rnsfernando/Smart-Soldering-Staion/Enclosure-Design/Design_1/1.jpg

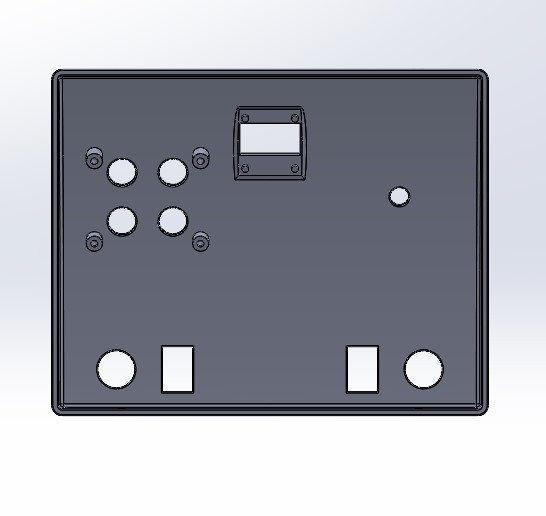
Enclosure-Design/Design_1/1.jpg
