rnsfernando/Smart-Soldering-Staion/Enclosure-Design/Design_1/2.jpg

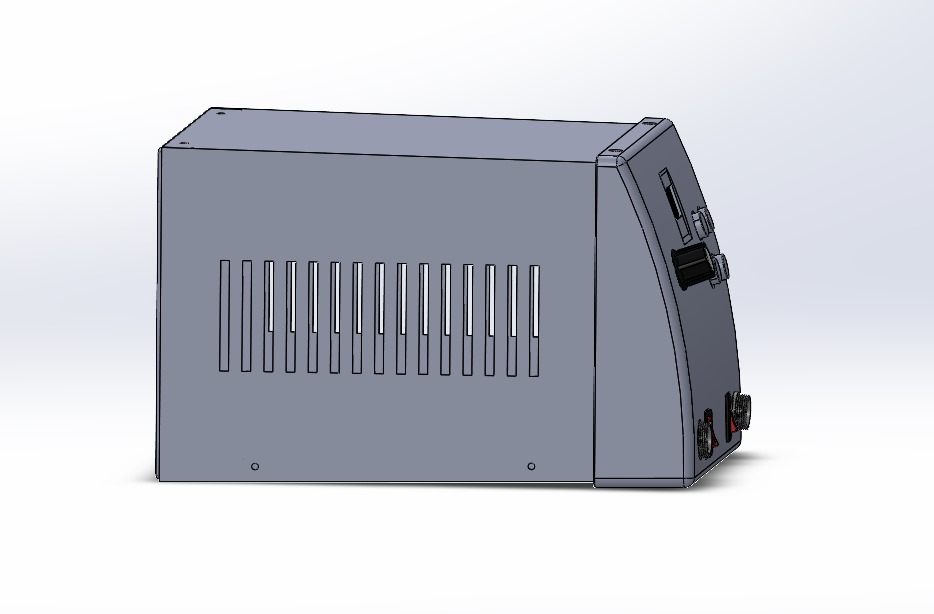
Enclosure-Design/Design_1/2.jpg
