rnsfernando/Smart-Soldering-Staion/Enclosure-Design/Design_1/3.jpg

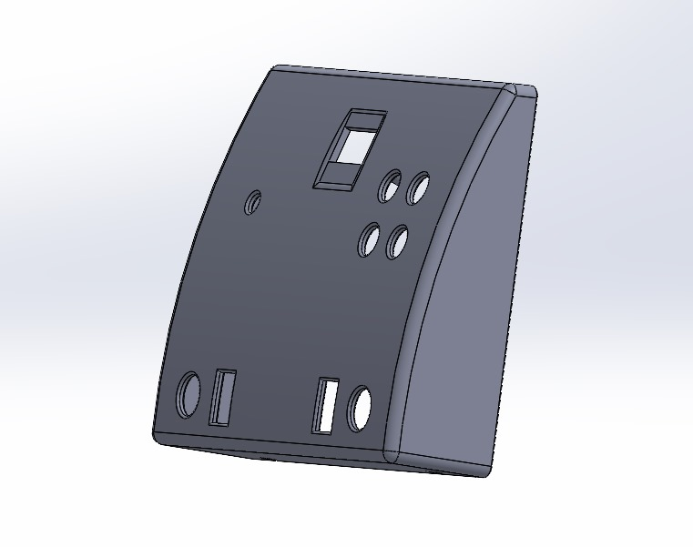
Enclosure-Design/Design_1/3.jpg
