rnsfernando/Smart-Soldering-Staion/Enclosure-Design/Design_1/4.jpg

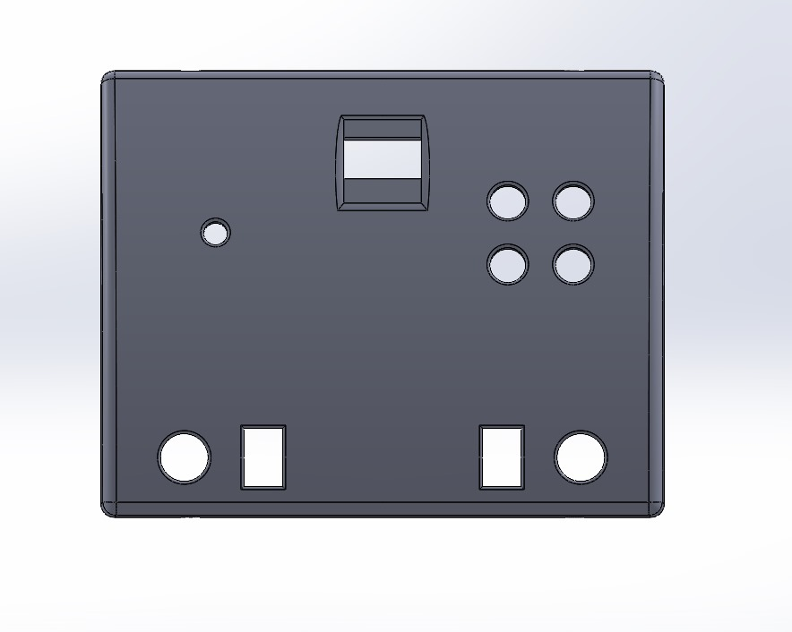
Enclosure-Design/Design_1/4.jpg
