rnsfernando/Smart-Soldering-Staion/Enclosure-Design/Design_1/5.jpg

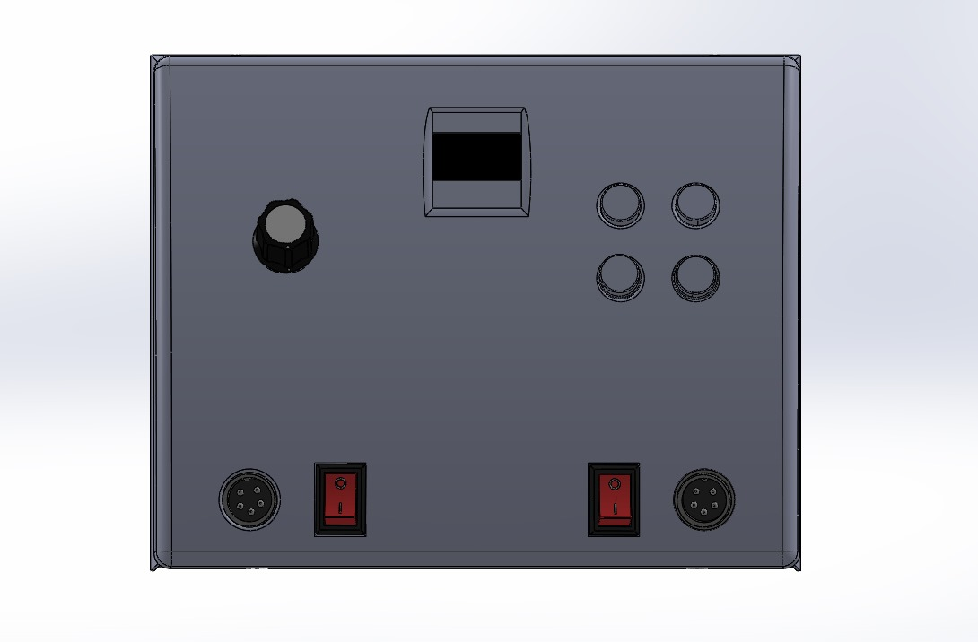
Enclosure-Design/Design_1/5.jpg
