rnsfernando/Smart-Soldering-Staion/Enclosure-Design/Design_2/1.png

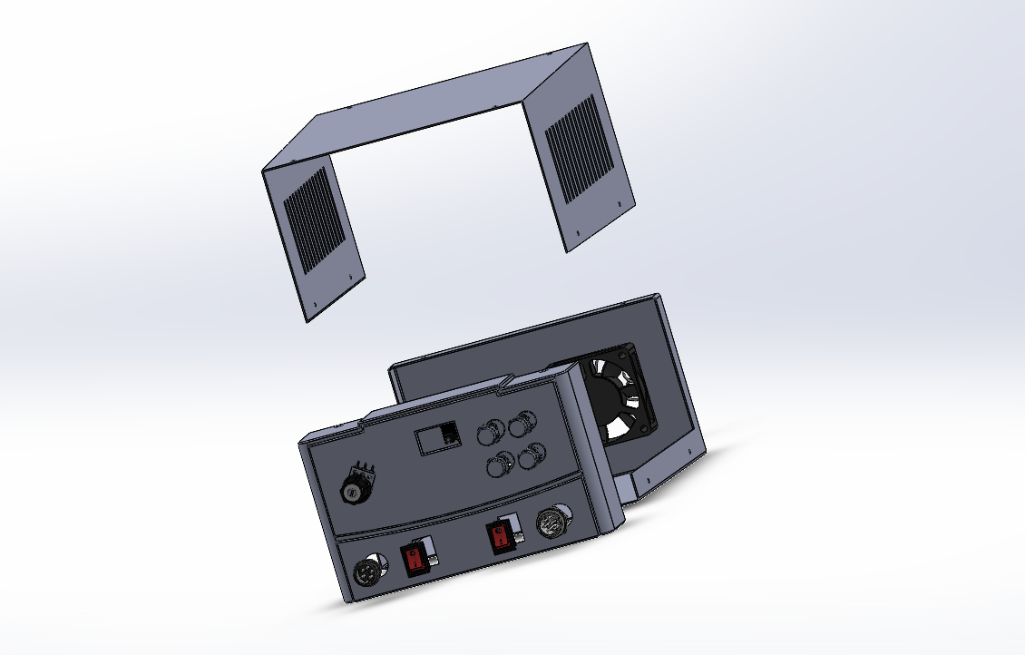
Enclosure-Design/Design_2/1.png
