rnsfernando/Smart-Soldering-Staion/Enclosure-Design/Design_2/2.png

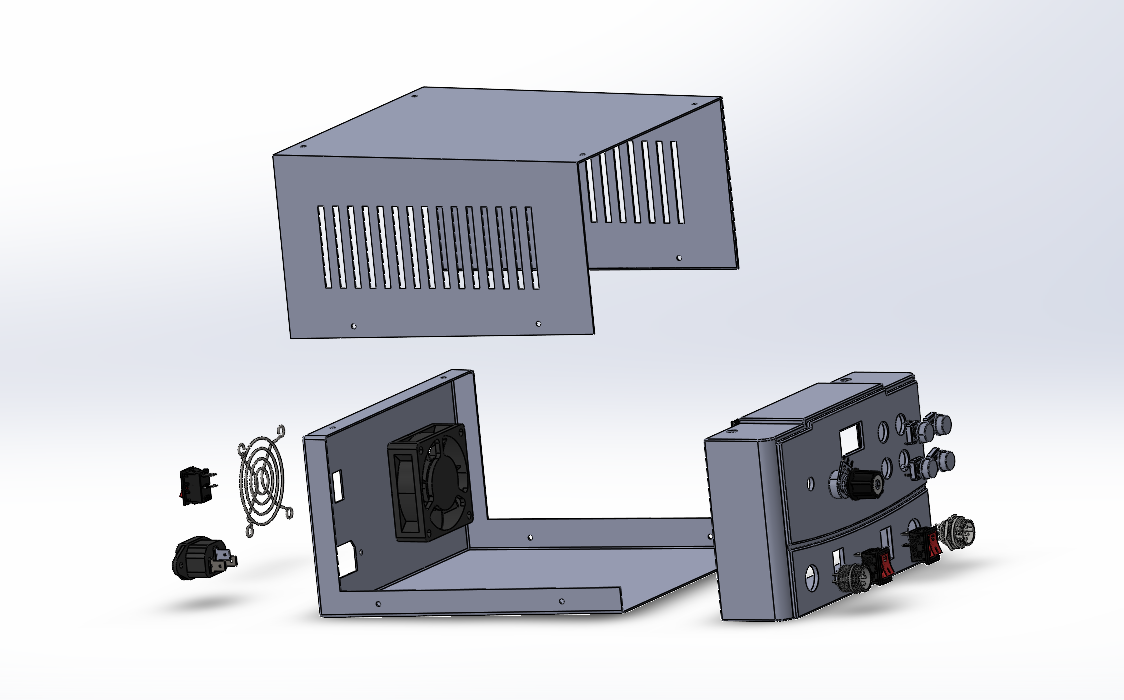
Enclosure-Design/Design_2/2.png
