rnsfernando/Smart-Soldering-Staion/Enclosure-Design/Design_2/3.png

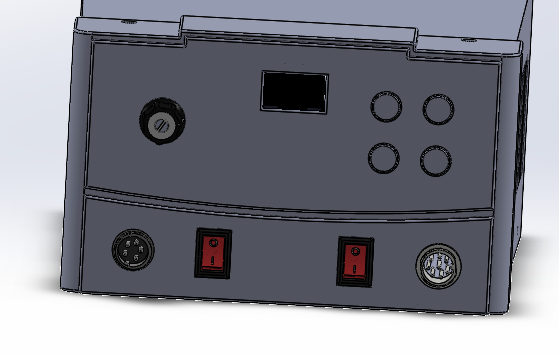
Enclosure-Design/Design_2/3.png
