rnsfernando/Smart-Soldering-Staion/Enclosure-Design/Design_2/4.png

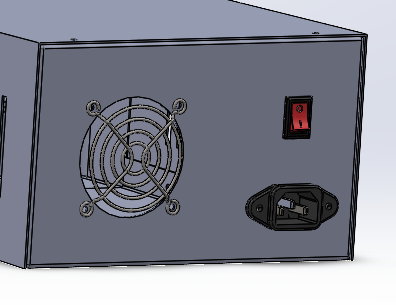
Enclosure-Design/Design_2/4.png
