rnsfernando/Smart-Soldering-Staion/Enclosure-Design/Design_2/5.png

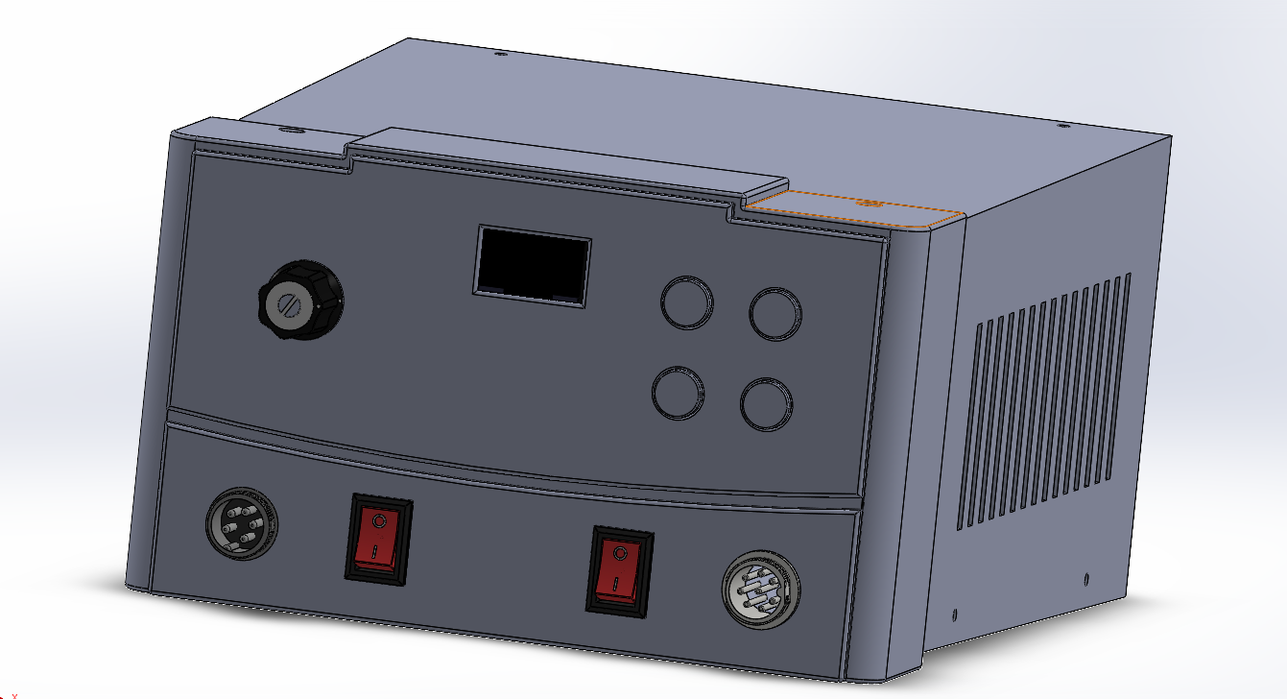
Enclosure-Design/Design_2/5.png
