rnsfernando/Smart-Soldering-Staion/images/Block-diagram.jpg

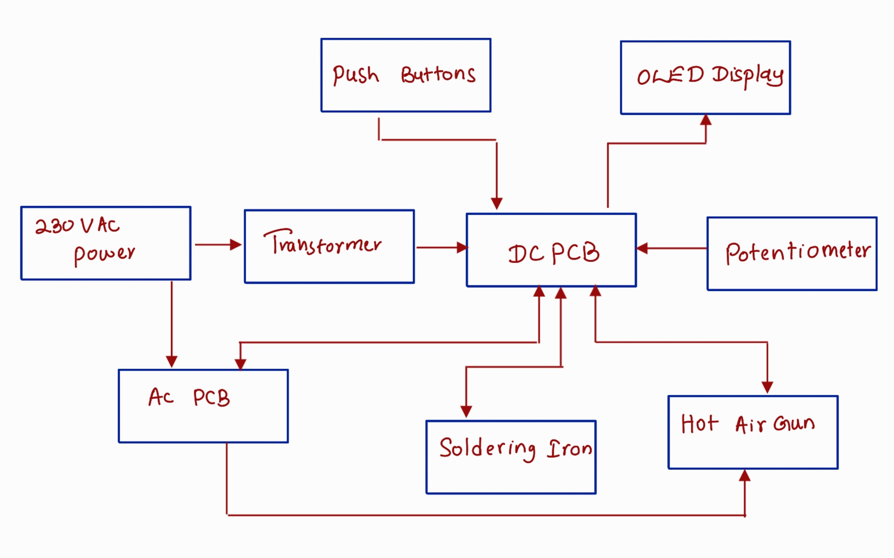
images/Block-diagram.jpg
