rnsfernando/Smart-Soldering-Staion/images/image.png

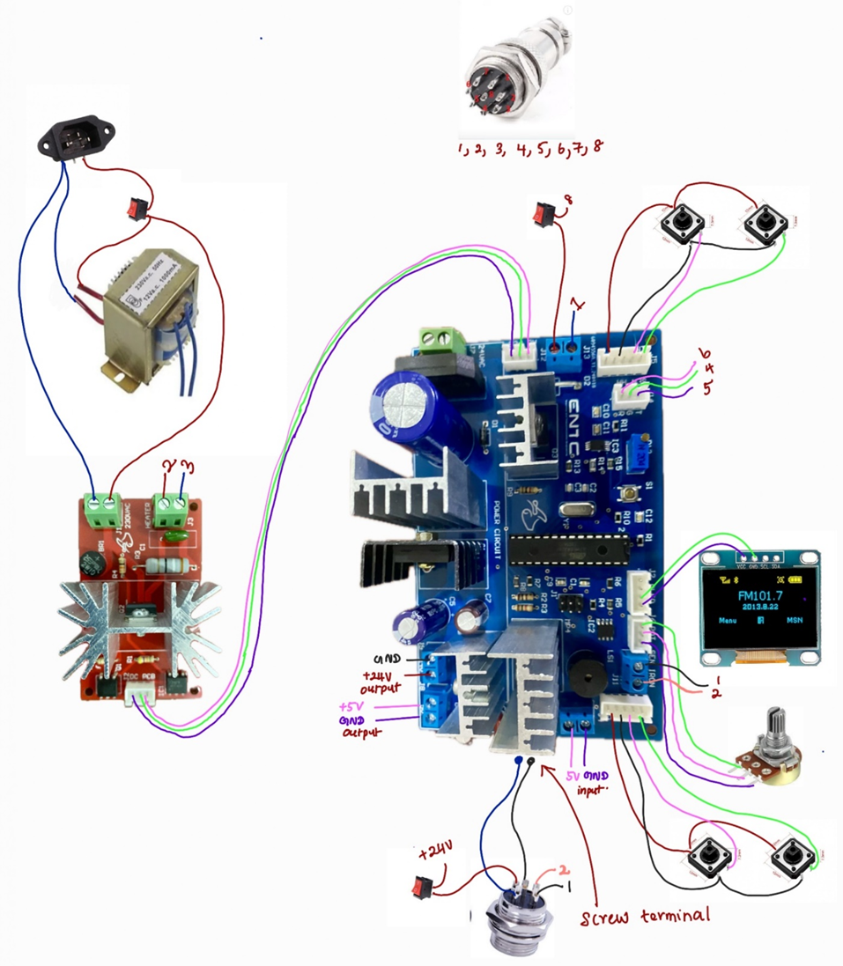
images/image.png
