rnsfernando/Smart-Soldering-Staion/images/IMG-20240630-WA0003.jpg

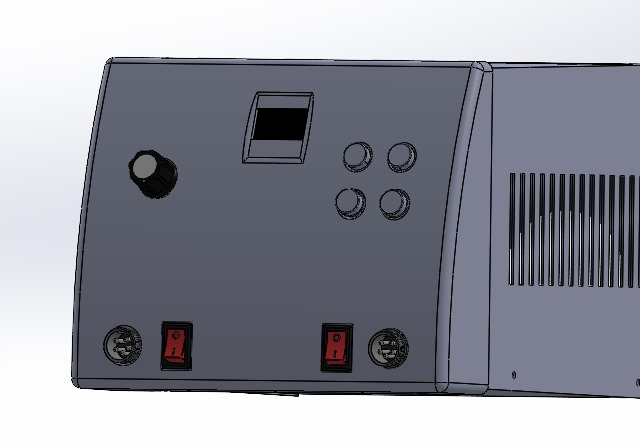
images/IMG-20240630-WA0003.jpg
