rnsfernando/Smart-Soldering-Staion/images/new_face_page-0001.jpg

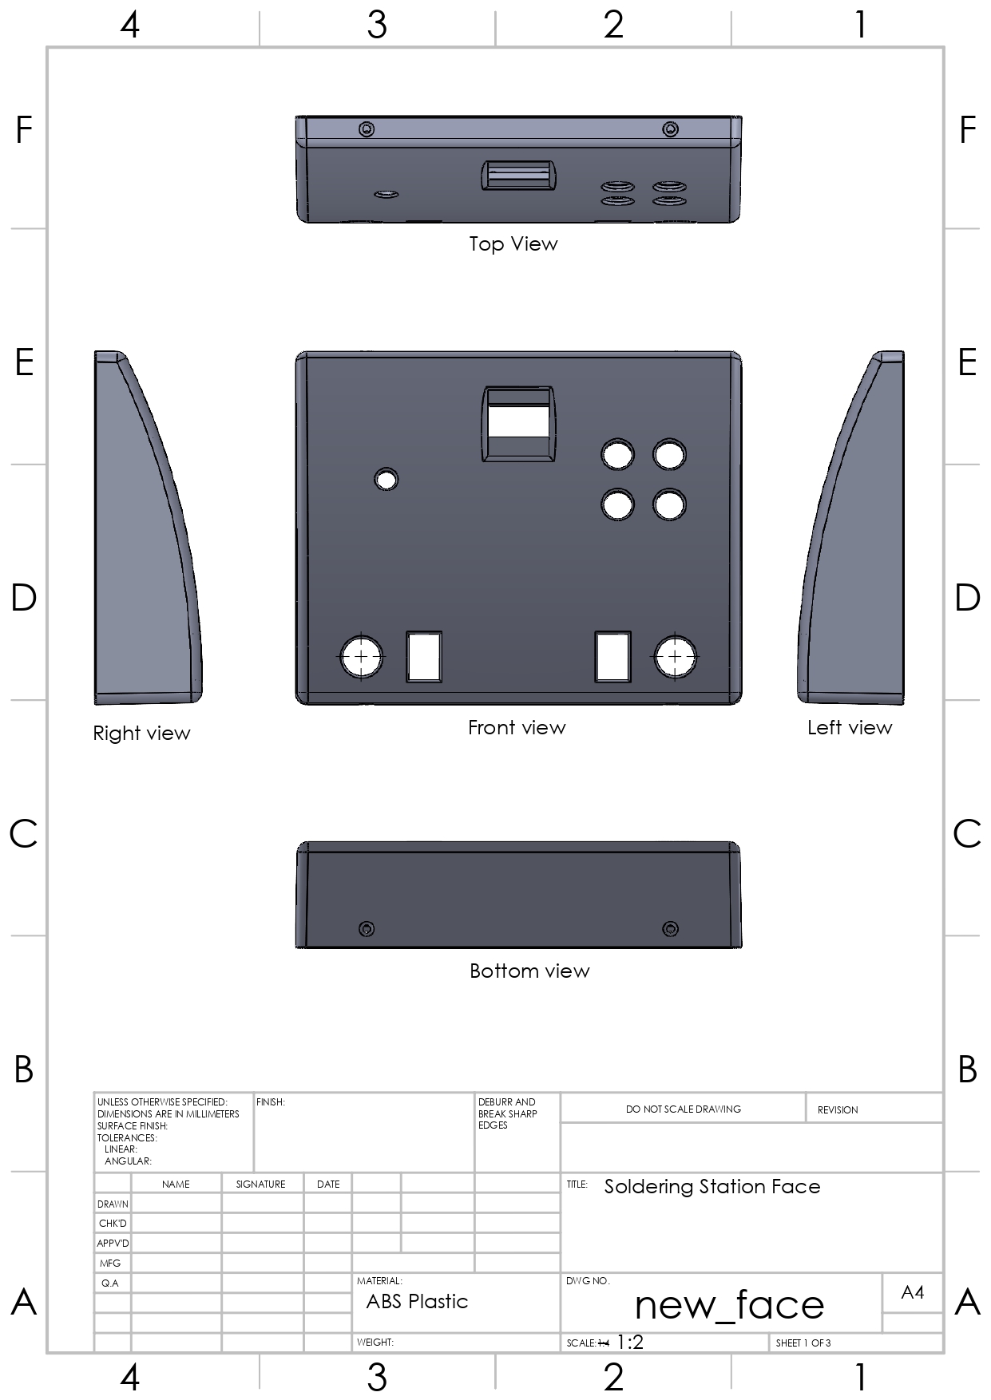
images/new_face_page-0001.jpg
