rnsfernando/Smart-Soldering-Staion/images/new_face_page-0003.jpg

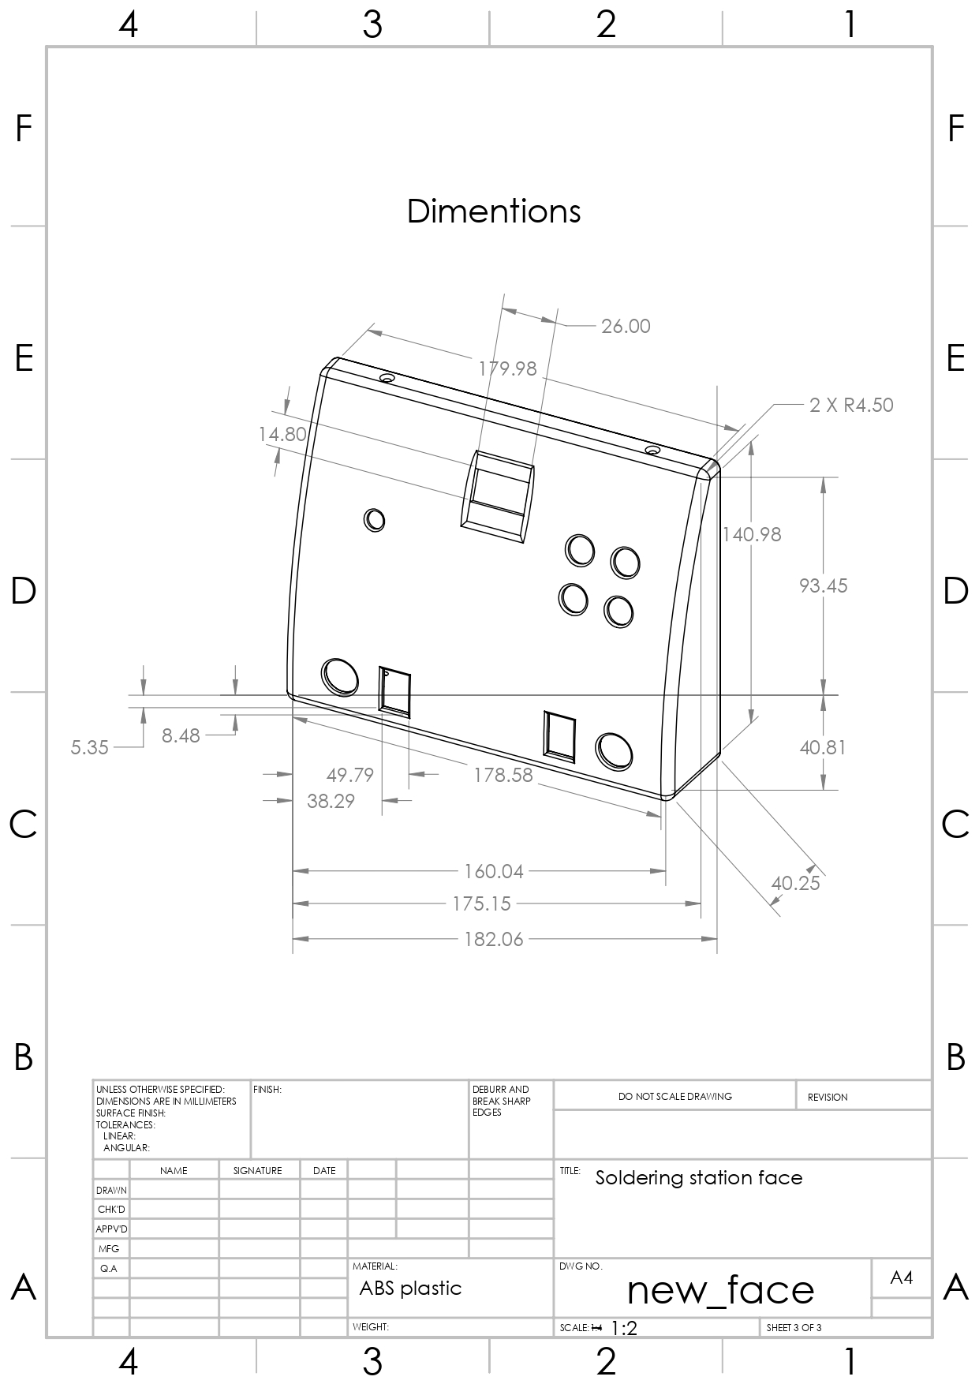
images/new_face_page-0003.jpg
